jankae/led-roomlamp/software/ledcontrol/command.h

#ifndef COMMAND_H_
#define COMMAND_H_

#include <stddef.h>
#include <stdlib.h>
#include <avr/pgmspace.h>
#include <avr/wdt.h>
#include "conversions.h"
#include "shell.h"
#include "uart.h"
#include "i2c.h"
#include "led.h"
#include "adc.h"

typedef void (*commandHandler_t) (uint8_t, char *[]);

typedef struct {
    char command[15];
    commandHandler_t command_function;
    char description[40];
} command_t;

void command_parse(uint8_t argc, char *argv[]);

uint8_t command_isMatch(const char *commandRAM, const char *compareFLASH);

void command_help(uint8_t argc, char *argv[]);
void command_reset(uint8_t argc, char *argv[]);
void command_time(uint8_t argc, char *argv[]);
void command_echo(uint8_t argc, char *argv[]);
void command_I2Cscan(uint8_t argc, char *argv[]);
void command_I2Cregister(uint8_t argc, char *argv[]);
void command_search(uint8_t argc, char *argv[]);
void command_ledstats(uint8_t argc, char *argv[]);
void command_ledset(uint8_t argc, char *argv[]);
void command_light(uint8_t argc, char *argv[]);
void command_whistle(uint8_t argc, char *argv[]);
void command_spectrum(uint8_t argc, char *argv[]);

#endif
